RBSC/MSX-EQ/Board/board.png

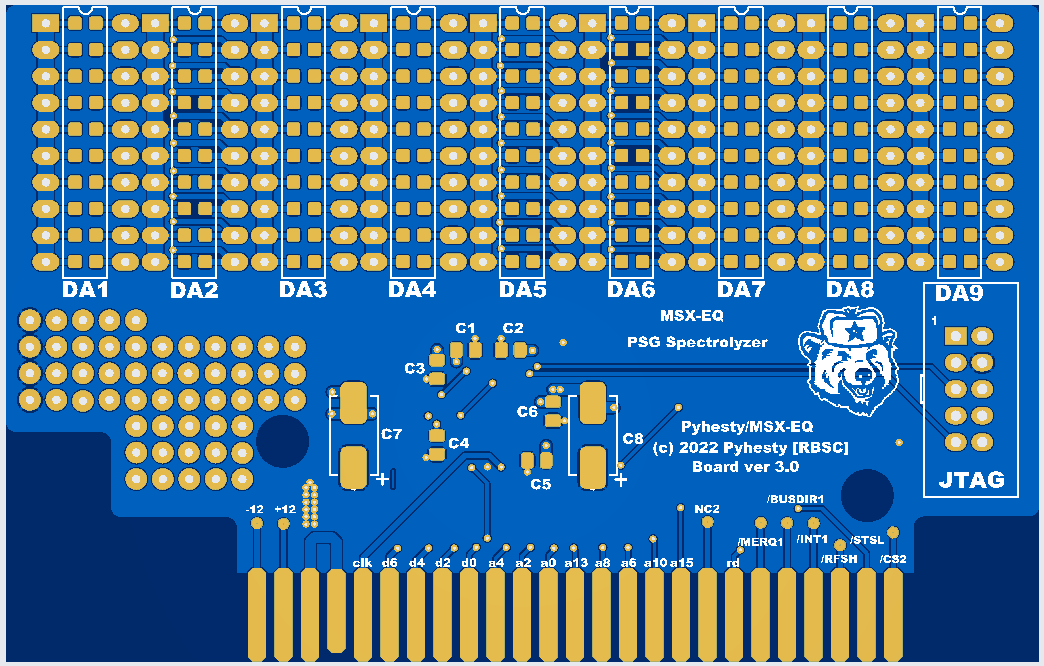
Board/board.png
