RBSC/MSX-EQ/Pics/MSX-EQ_Demo.jpg

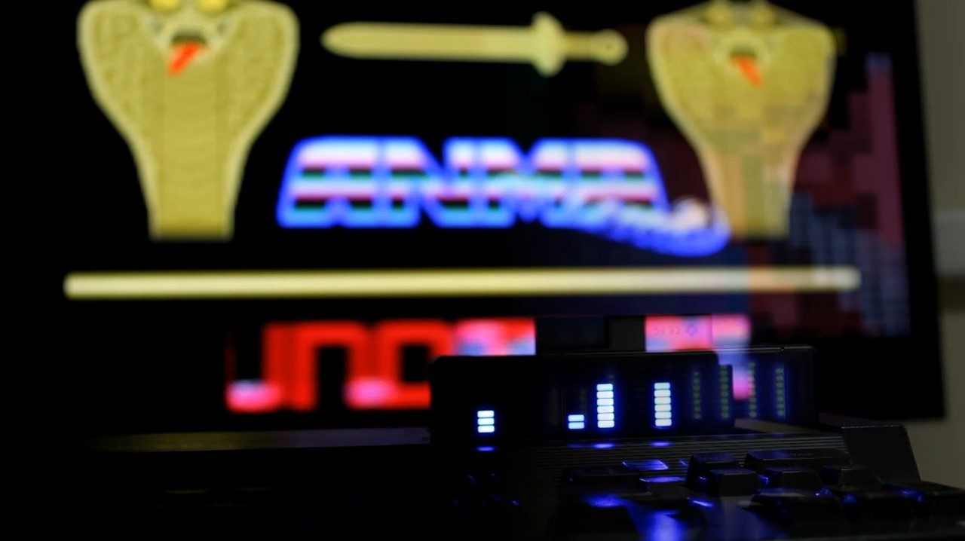
Pics/MSX-EQ_Demo.jpg
